pdaehne/TL866-FlashROM-Adapter/images/Xgpro_Load_Diag_100000.png

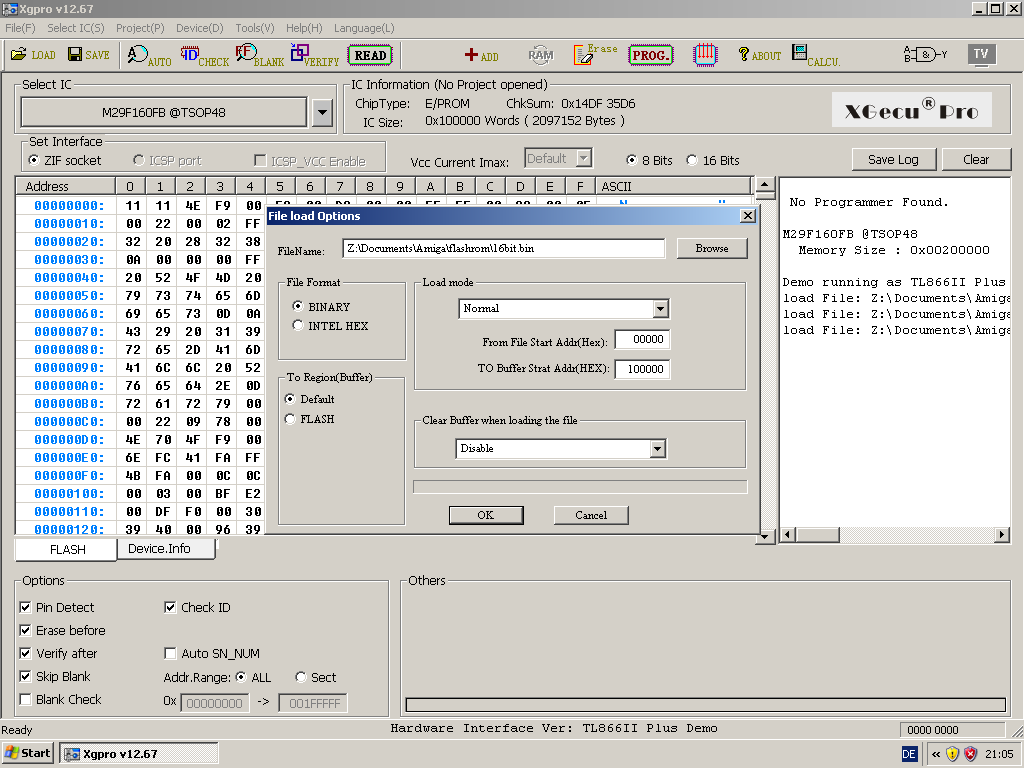
images/Xgpro_Load_Diag_100000.png
