pdaehne/TL866-FlashROM-Adapter/images/Xgpro_Select_Device.png

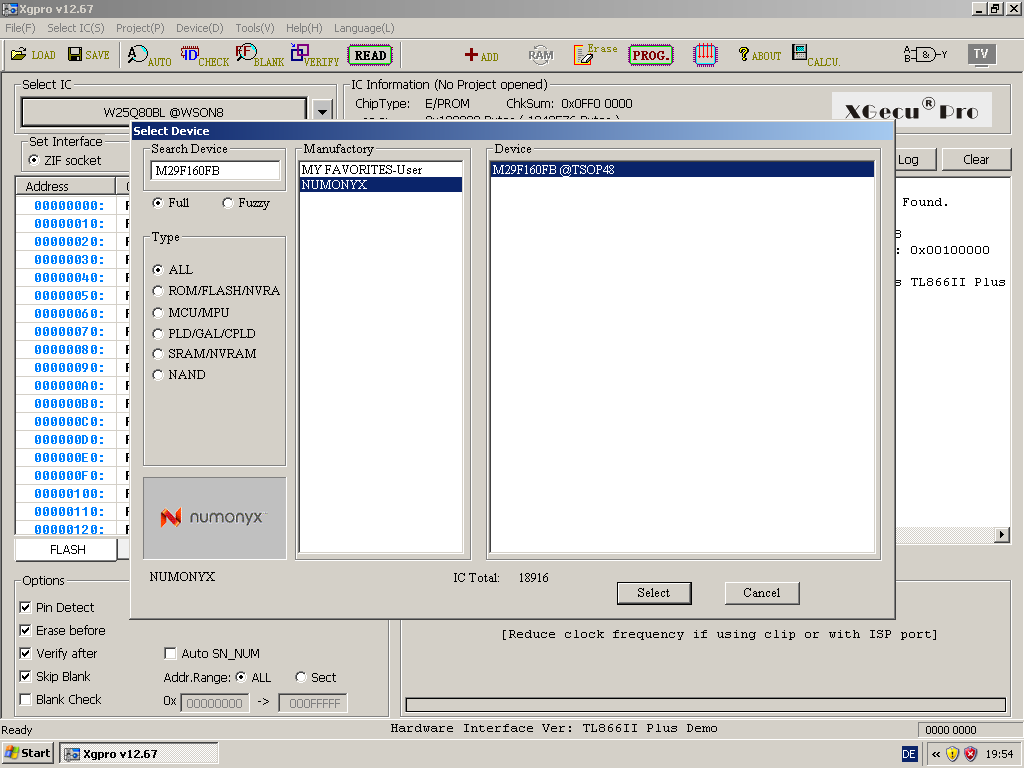
images/Xgpro_Select_Device.png
